idooley/AnalogCrossover/ltspice-simulations/input-stage-ltspice.asc

C1: cap; 220pF
C2: cap; 220nF
C3: cap; 220nF
C4: cap; 220nF
C5: cap; 22µ
C6: cap; 2.2n
C7: cap; 2.2n
C8: cap; 2.2n
R1: res; 200k
R2: res; 100k
R3: res; 1k
R4: res; 3.32k
R5: res; 30k
R6: res; 12k
R7: res; 180k
R8: res; 2.2k
R9: res; 1k
R10: res; 2.2k
U1: opamp
U9: opamp
V4: voltage; ""; AC 1
Named nets: 0, out, In
.ac dec 500 10 40000
.lib opamp.sub
