idooley/AnalogCrossover/ltspice-simulations/lowpass-ltspice.asc

C1: cap; 112nF
C2: cap; 112nF
C3: cap; 56nF
C5: cap; 56nF
R1: res; 774.19
R2: res; 717.24
R3: res; 774.19
R9: res; 717.24
U1: opamp
U9: opamp
V4: voltage; ""; AC 1
Named nets: 0, out, In
.ac dec 500 10 40000
.lib opamp.sub
